ArgonautGit/wallet_dmm/docs/simulation/volts.png

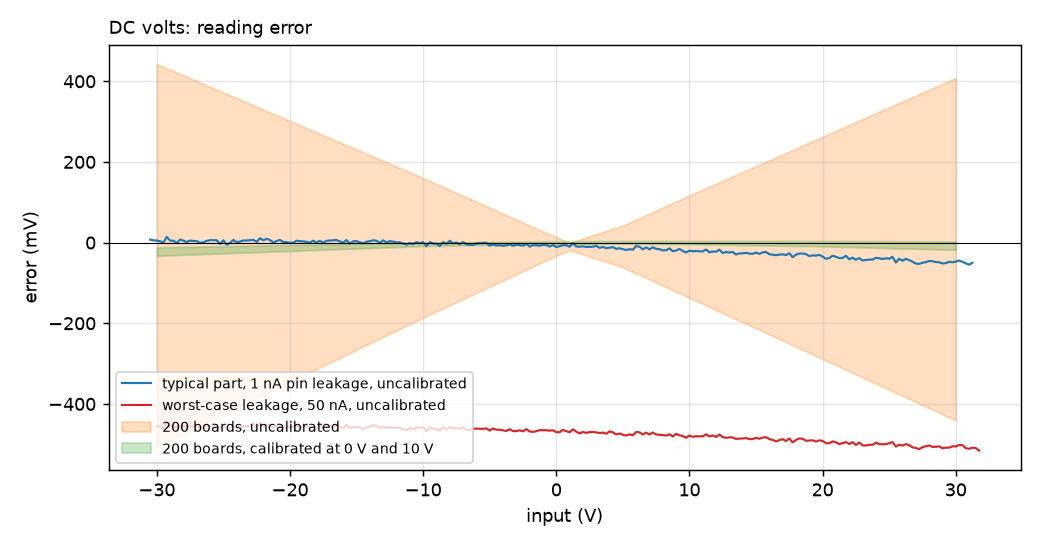
docs/simulation/volts.png
