ArgonautGit/wallet_dmm/scripts/sexpr.py

"""Minimal reader/writer for KiCad S-expression files."""

import re

_TOKEN = re.compile(r'\s*(?:(\()|(\))|("(?:[^"\\]|\\.)*")|([^\s()"]+))')


class Sym(str):
    """An unquoted atom."""


def parse(text: str):
    stack = [[]]
    pos = 0
    n = len(text)
    while pos < n:
        m = _TOKEN.match(text, pos)
        if not m:
            if text[pos:].strip() == "":
                break
            raise ValueError(f"bad token at {pos}: {text[pos:pos + 40]!r}")
        pos = m.end()
        if m.group(1):
            stack.append([])
        elif m.group(2):
            done = stack.pop()
            stack[-1].append(done)
        elif m.group(3) is not None:
            s = m.group(3)[1:-1]
            stack[-1].append(s.replace('\\"', '"').replace("\\\\", "\\"))
        else:
            stack[-1].append(Sym(m.group(4)))
    return stack[0][0]


def _atom(x):
    if isinstance(x, Sym):
        return str(x)
    if isinstance(x, bool):
        return "yes" if x else "no"
    if isinstance(x, (int, float)):
        return fmt_num(x)
    s = str(x).replace("\\", "\\\\").replace('"', '\\"').replace("\n", "\\n")
    return f'"{s}"'


def fmt_num(v):
    if isinstance(v, int):
        return str(v)
    s = f"{v:.6f}".rstrip("0").rstrip(".")
    return "0" if s in ("-0", "") else s


def dump(node, indent=0) -> str:
    if not isinstance(node, list):
        return _atom(node)
    if all(not isinstance(c, list) for c in node) or (
        node and node[0] in ("xy", "at", "size", "start", "end", "center", "mid", "pts_inline")
    ):
        return "(" + " ".join(dump(c) for c in node) + ")"
    head = []
    rest = []
    for i, c in enumerate(node):
        if isinstance(c, list):
            rest = node[i:]
            break
        head.append(c)
    pad = "\t" * (indent + 1)
    out = "(" + " ".join(_atom(h) for h in head)
    for c in rest:
        out += "\n" + pad + dump(c, indent + 1)
    return out + "\n" + "\t" * indent + ")"


def find(node, key):
    """First child list whose head is key."""
    for c in node:
        if isinstance(c, list) and c and c[0] == key:
            return c
    return None


def find_all(node, key):
    return [c for c in node if isinstance(c, list) and c and c[0] == key]
